PrateekIITMandi/Autonomous_Drone/pixhawk plate.SLDPRT

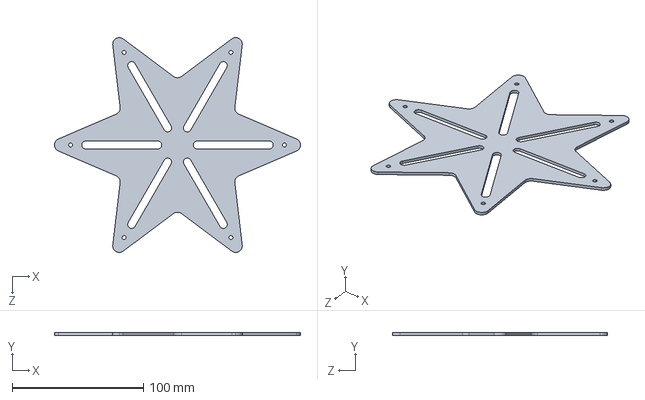
[picture p20: CAD file, 2025-11-21]
pixhawk plate.SLDPRT
187.6 x 2.00 x 163.9 mm
