PrateekIITMandi/Autonomous_Drone/motor_casing.SLDPRT

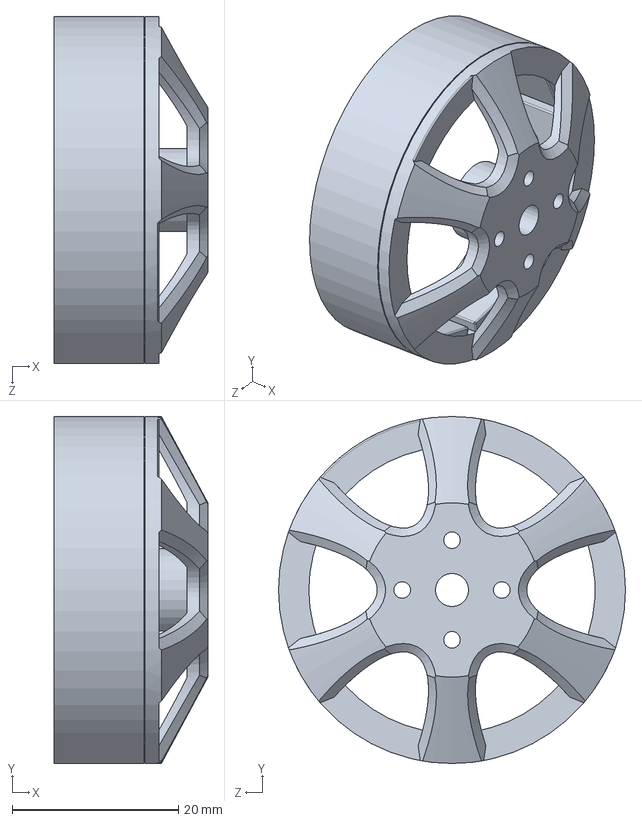
[picture p21: CAD file, 2025-11-21]
motor_casing.SLDPRT
18.5 x 41.8 x 41.8 mm
