PrateekIITMandi/Autonomous_Drone/bracket.SLDPRT

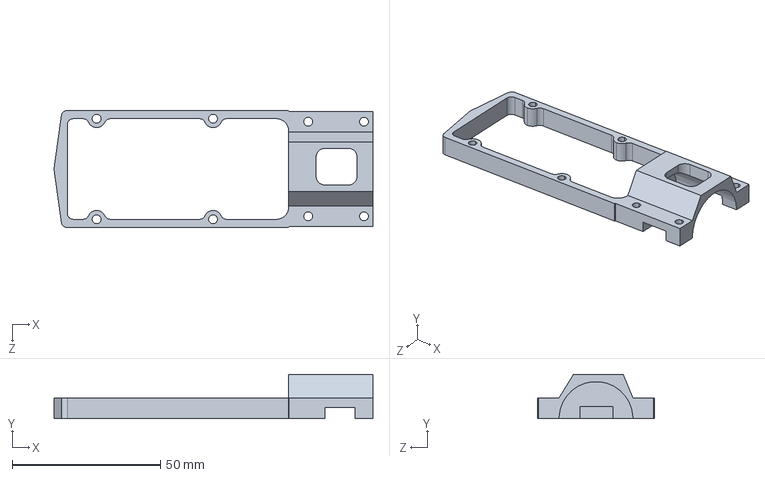
[picture p22: CAD file, 2025-11-21]
bracket.SLDPRT
107.5 x 14.9 x 39.5 mm
