PrateekIITMandi/Autonomous_Drone/leg connector.SLDPRT

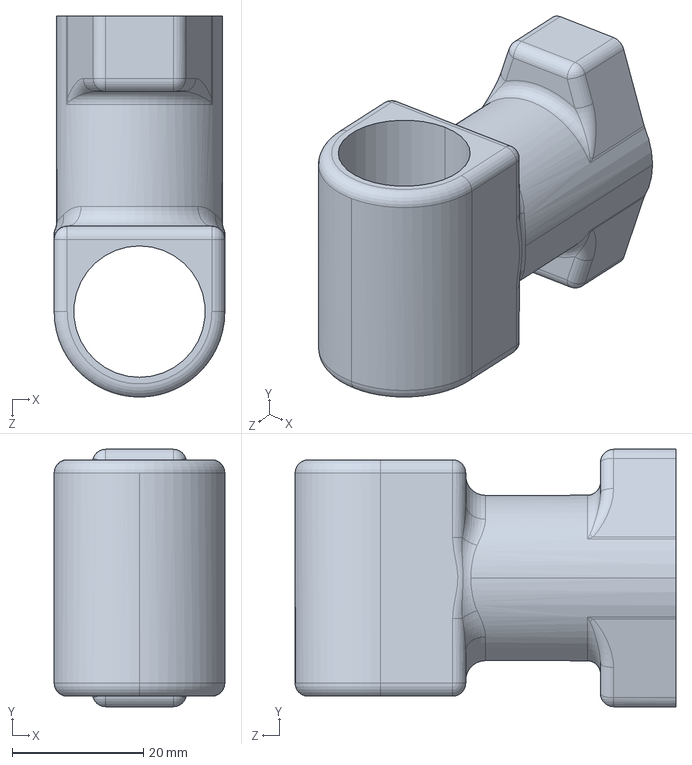
[picture p23: CAD file, 2025-11-21]
leg connector.SLDPRT
26.0 x 39.2 x 58.0 mm
