PrateekIITMandi/Autonomous_Drone/leg pivot.SLDPRT

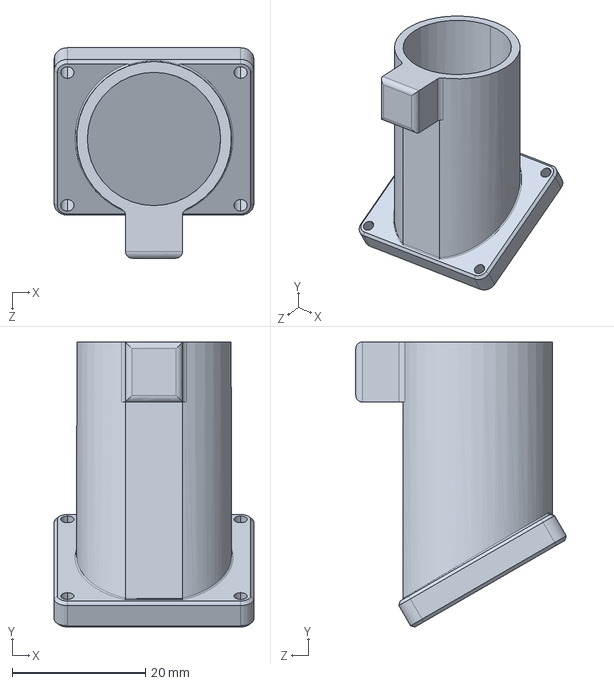
[picture p24: CAD file, 2025-11-21]
leg pivot.SLDPRT
30.0 x 42.8 x 31.6 mm
