PrateekIITMandi/Autonomous_Drone/propeller.SLDPRT

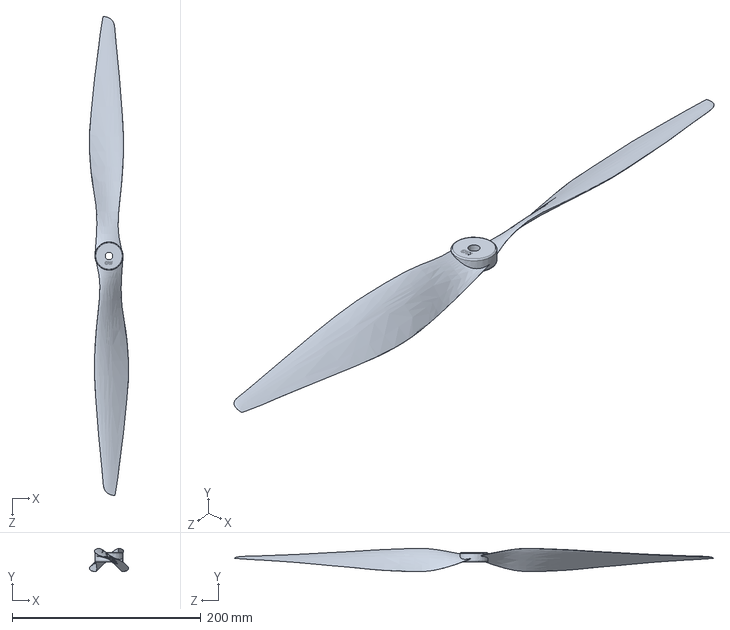
[picture p25: CAD file, 2025-11-21]
propeller.SLDPRT
41.7 x 24.7 x 508.0 mm
