PrateekIITMandi/Autonomous_Drone/top plate.SLDPRT

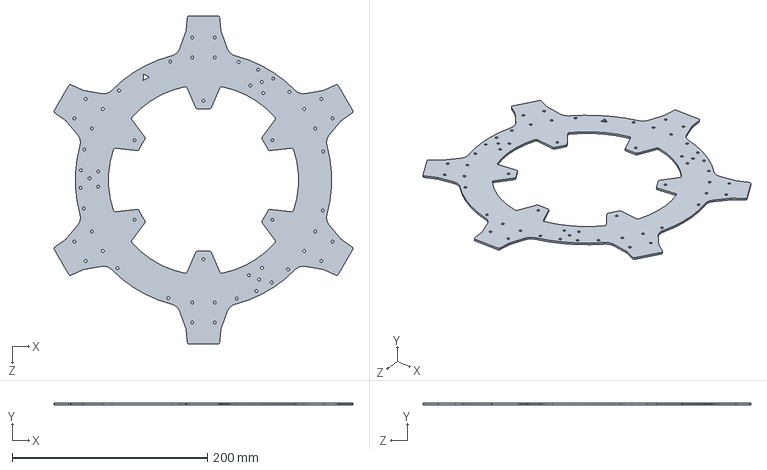
[picture p26: CAD file, 2025-11-21]
top plate.SLDPRT
306.5 x 2.00 x 336.4 mm
