PrateekIITMandi/Autonomous_Drone/fine tuning/fine_tuning/data/before_vs_after.png

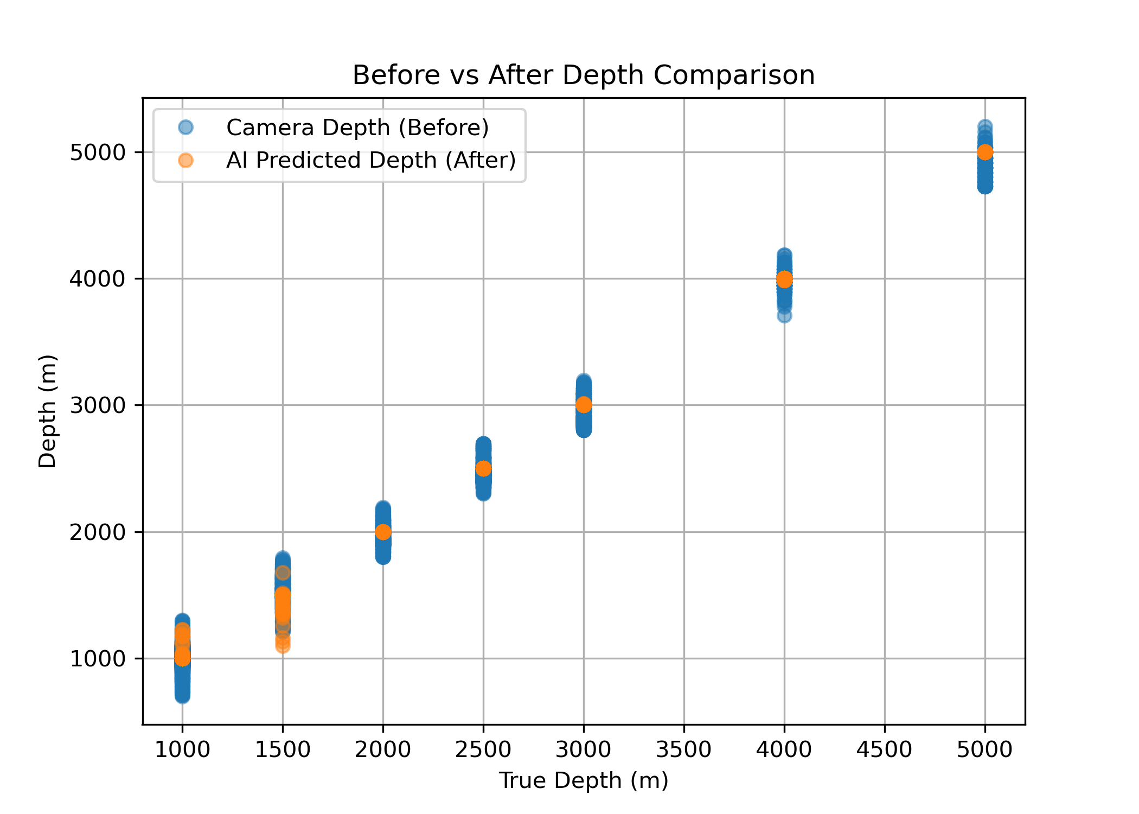
fine tuning/fine_tuning/data/before_vs_after.png
