PrateekIITMandi/Autonomous_Drone/fine tuning/fine_tuning/data/true_vs_camera.png

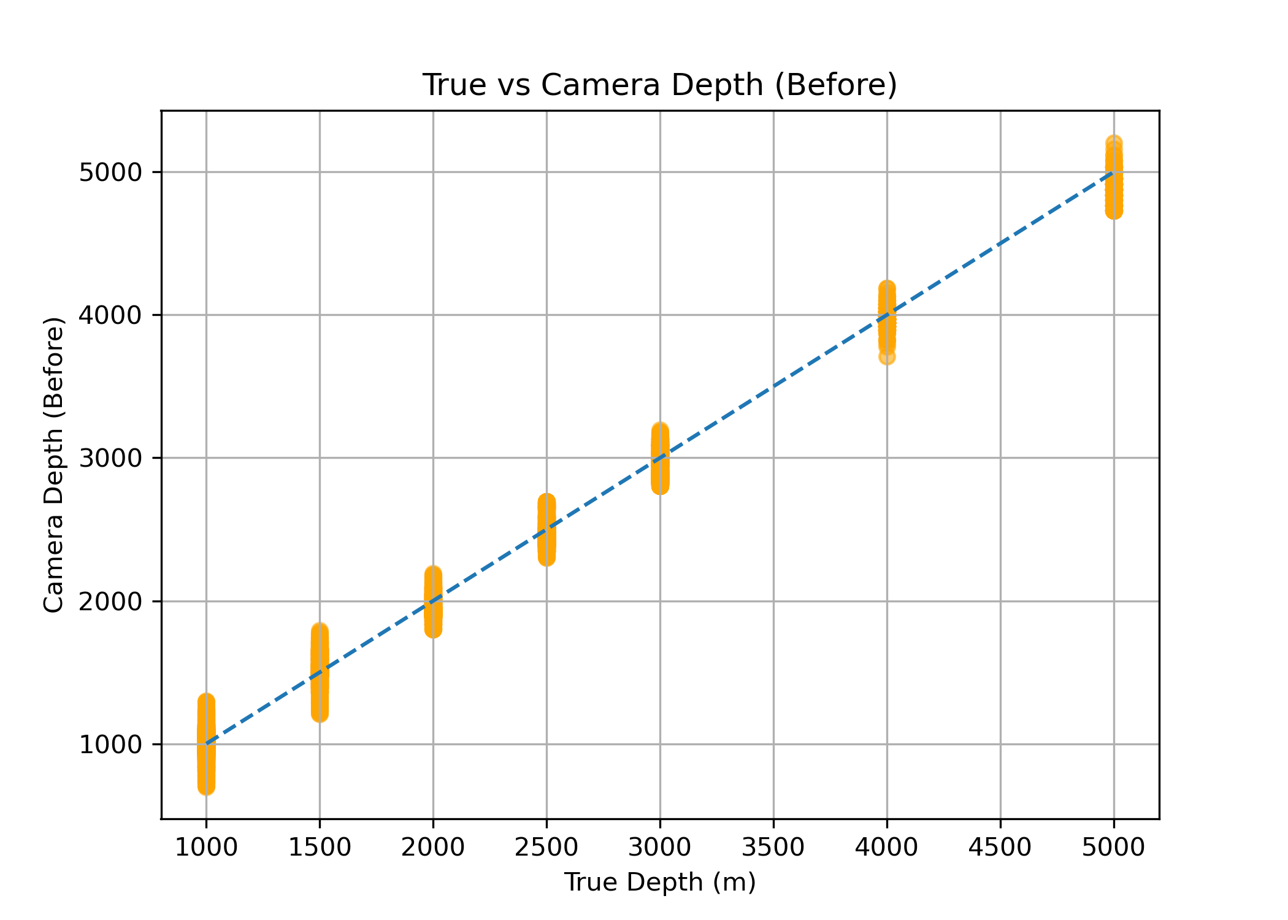
fine tuning/fine_tuning/data/true_vs_camera.png
